Zappes/avr-Schlangomat/Firmware/Schlangomat.h

/*
 LUFA Library
 Copyright (C) Dean Camera, 2014.

 dean [at] fourwalledcubicle [dot] com
 www.lufa-lib.org
 */

/*
 Copyright 2014  Dean Camera (dean [at] fourwalledcubicle [dot] com)

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
 The author disclaims all warranties with regard to this
 software, including all implied warranties of merchantability
 and fitness.  In no event shall the author be liable for any
 special, indirect or consequential damages or any damages
 whatsoever resulting from loss of use, data or profits, whether
 in an action of contract, negligence or other tortious action,
 arising out of or in connection with the use or performance of
 this software.
 */

/** \file
 *
 *  Header file for VirtualSerial.c.
 */

#ifndef _SCHLANGOMAT_H_
#define _SCHLANGOMAT_H_

#define SENSOR_INTERVAL_SECS 15

#include <avr/io.h>
#include <avr/interrupt.h>
#include <util/delay.h>
#include <string.h>
#include <stdio.h>
#include <stdlib.h>
#include <stdbool.h>

#include "lib/esp.h"
#include "lib/usb.h"
#include "lib/am2302.h"
#include "lib/relay.h"
#include "lib/rules.h"
#include "lib/parser.h"
#include "lib/sensors.h"
#include "lib/timer.h"

#endif
